gerb-ster/Vulcan-DCO/images/attiny programmer.jpeg

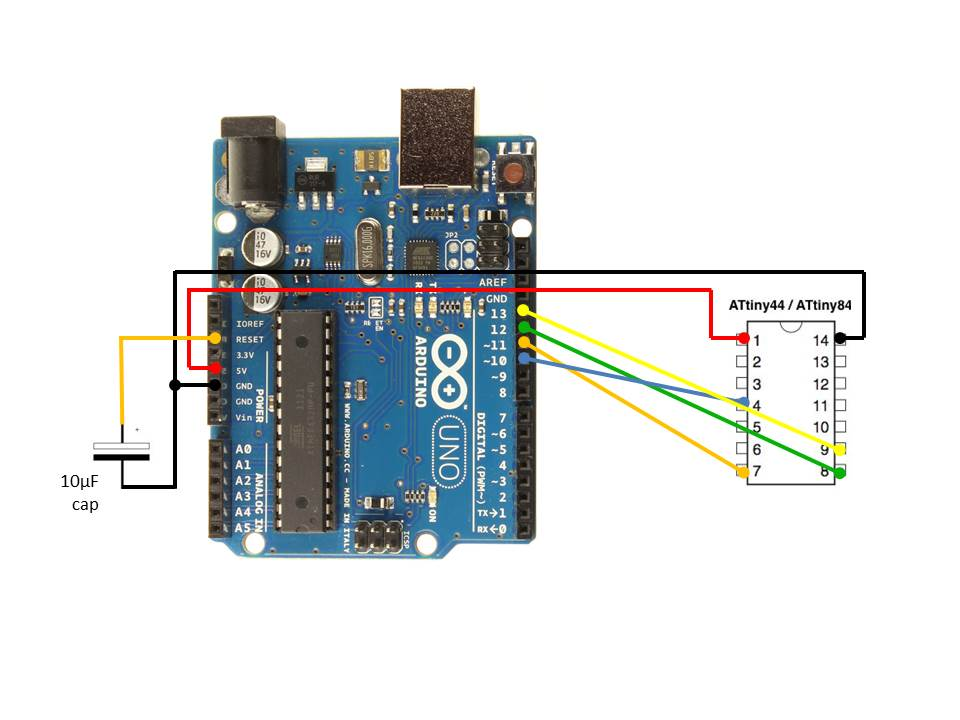
images/attiny programmer.jpeg
