gerb-ster/Vulcan-DCO/images/IMG_1315.jpeg

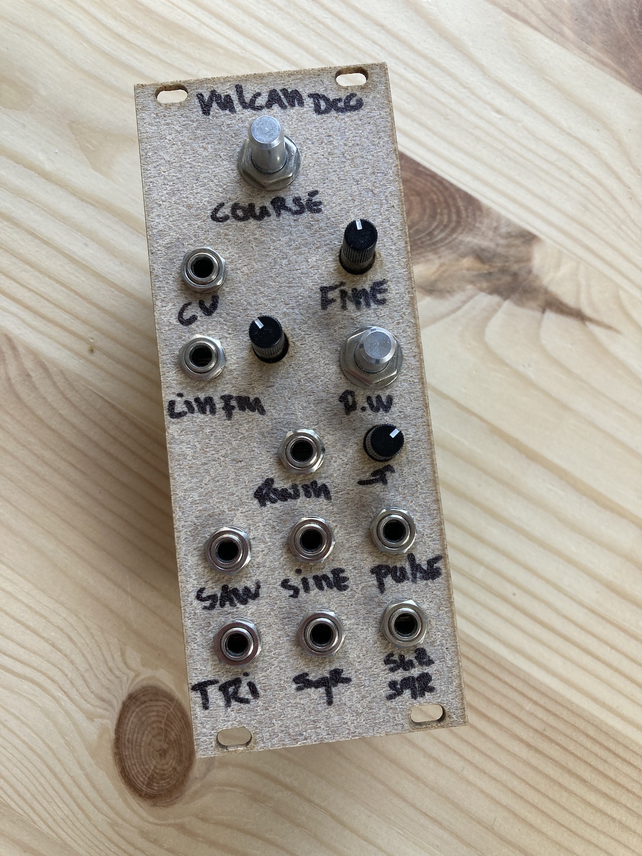
images/IMG_1315.jpeg
