gerb-ster/Vulcan-DCO/images/IMG_1316.jpeg

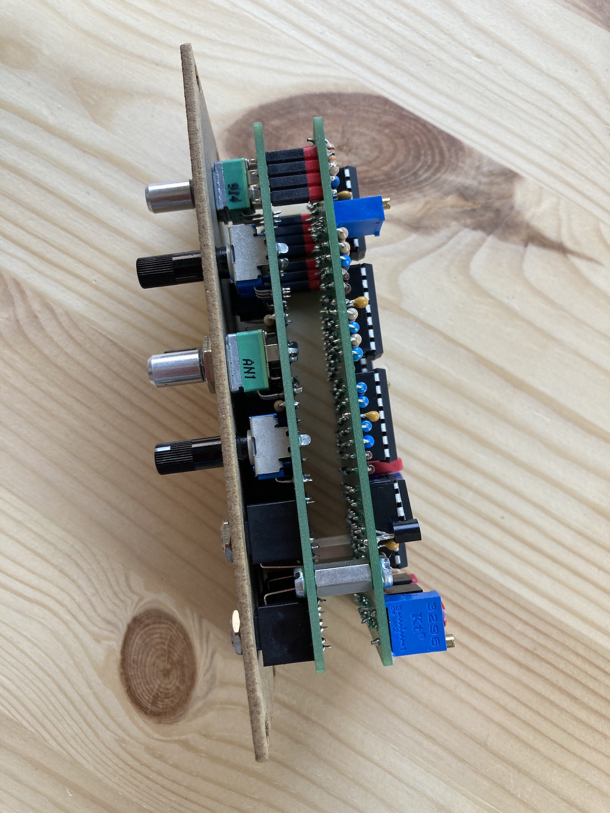
images/IMG_1316.jpeg
