gerb-ster/Vulcan-DCO/images/IMG_1317.jpeg

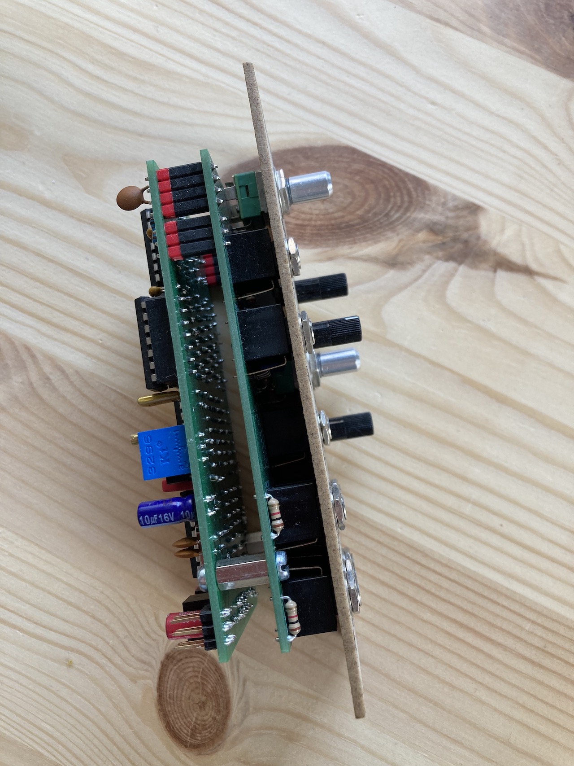
images/IMG_1317.jpeg
