gerb-ster/Vulcan-DCO/images/IMG_1318.jpeg

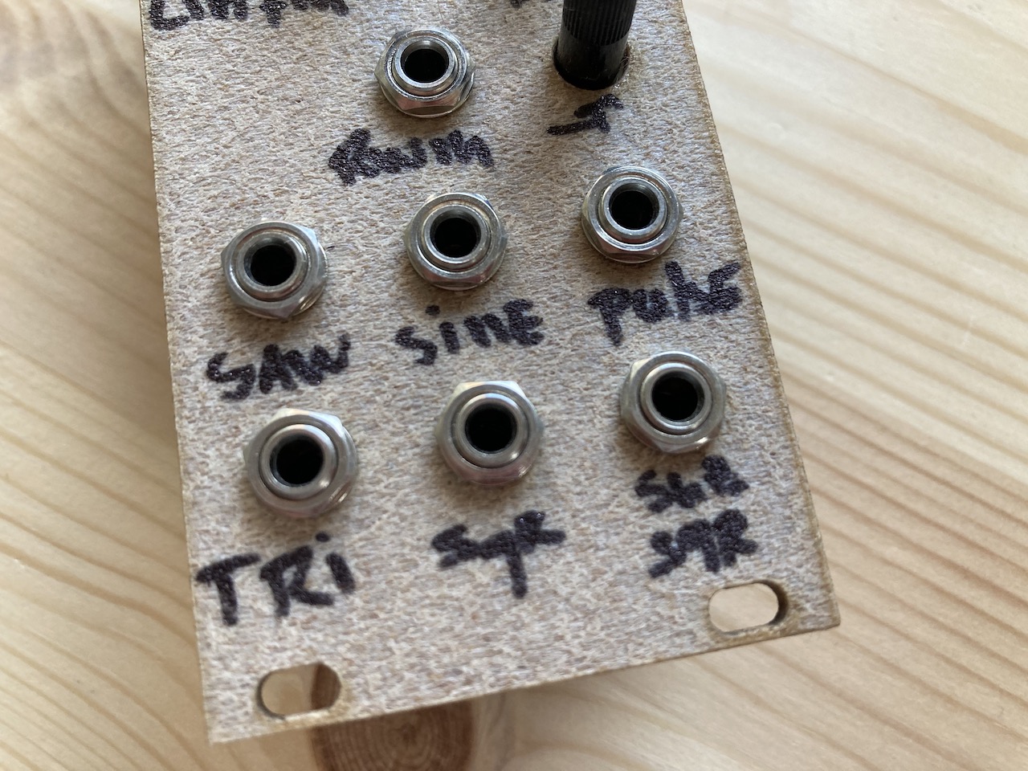
images/IMG_1318.jpeg
