gerb-ster/Vulcan-DCO/images/IMG_1319.jpeg

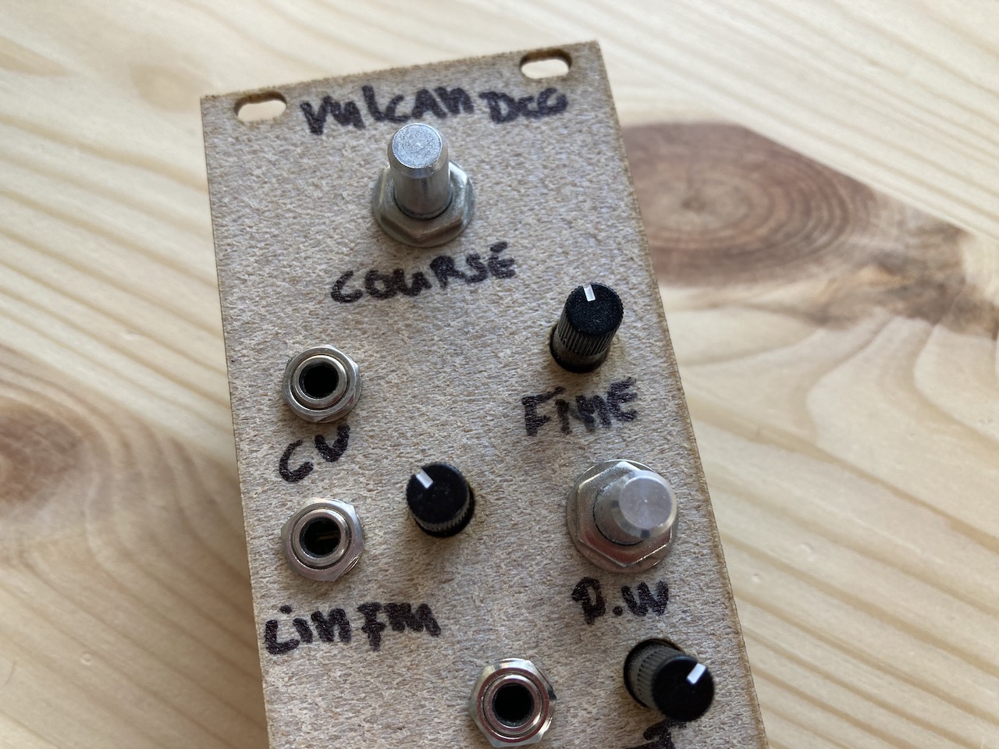
images/IMG_1319.jpeg
