gerb-ster/Vulcan-DCO/images/IMG_1320.jpeg

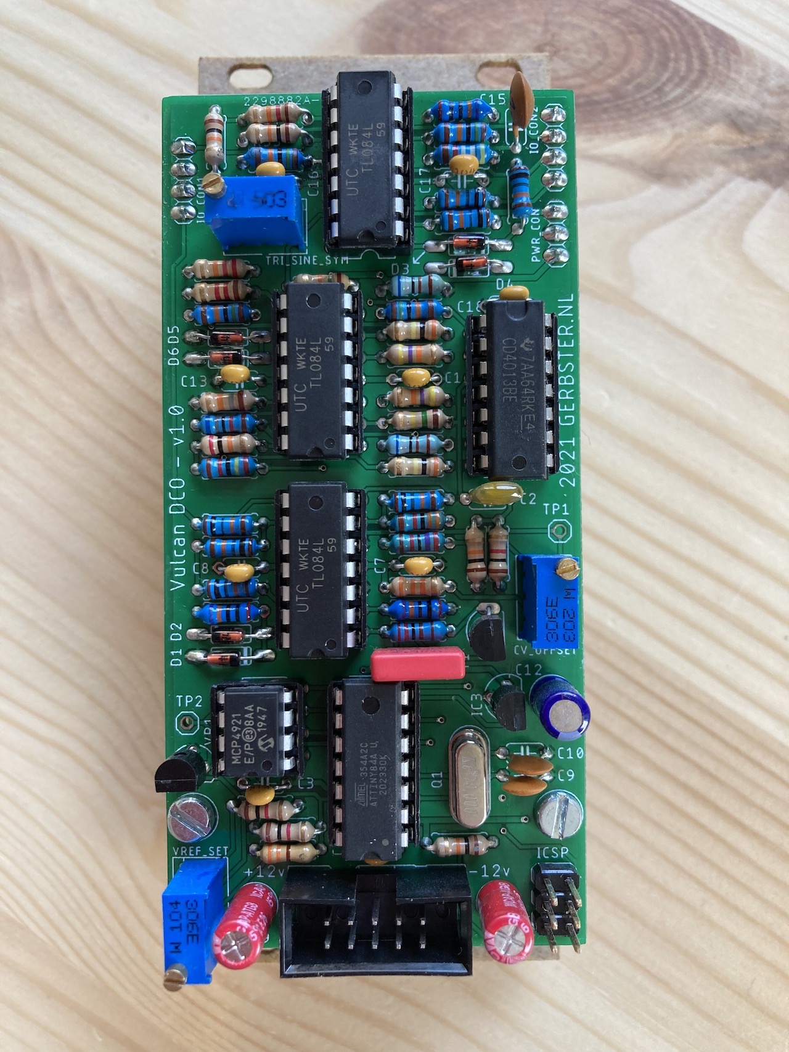
images/IMG_1320.jpeg
