gerb-ster/Vulcan-DCO/images/IMG_1321.jpeg

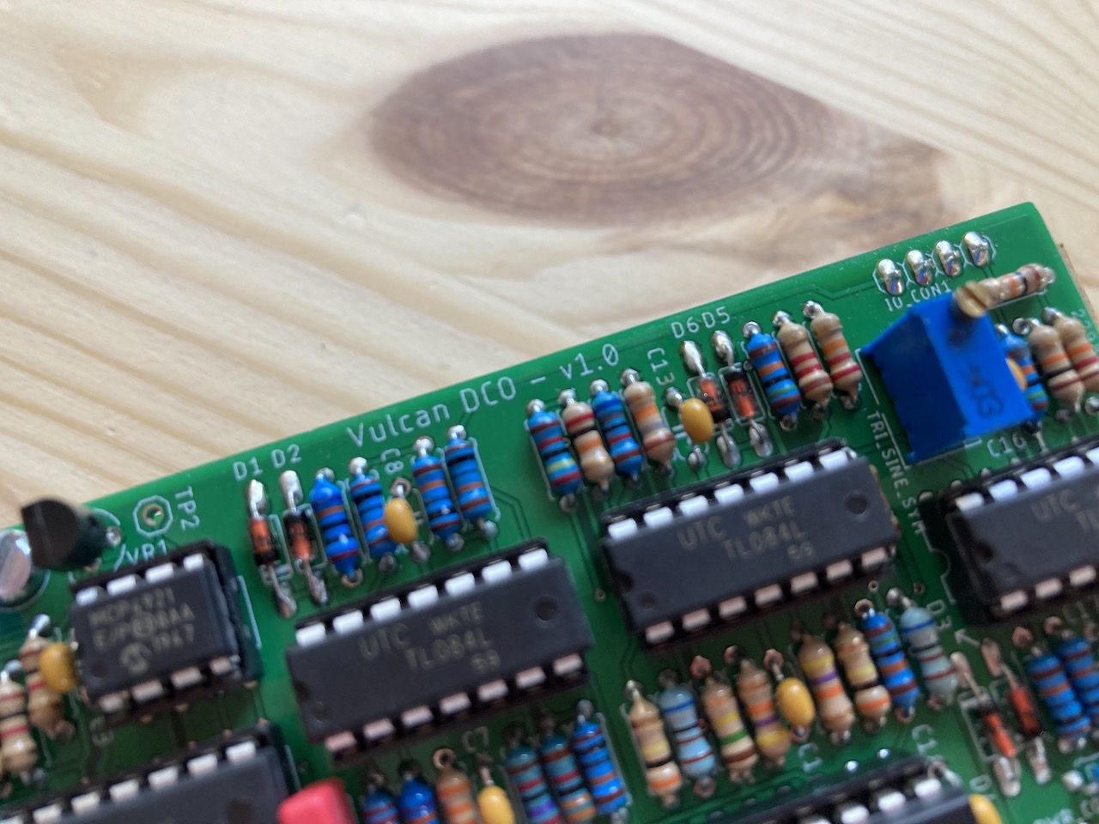
images/IMG_1321.jpeg
