gerb-ster/Vulcan-DCO/images/IMG_1322.jpeg

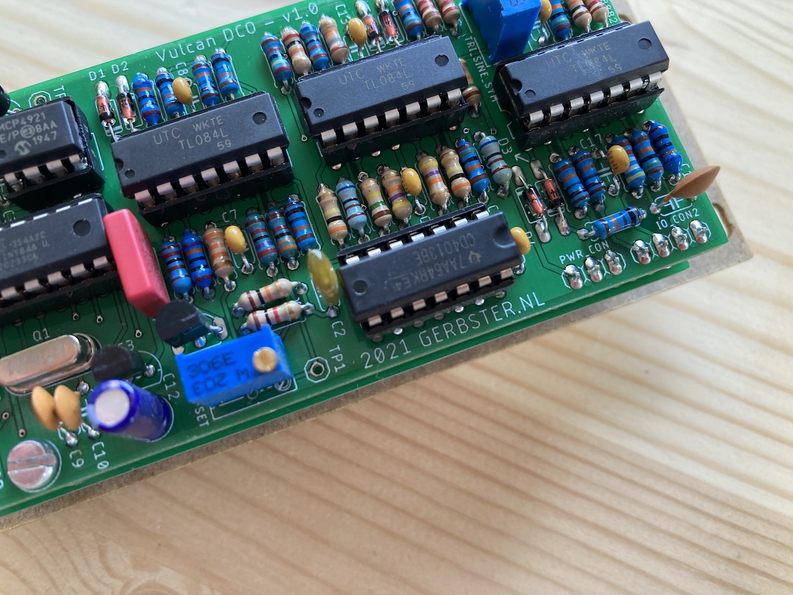
images/IMG_1322.jpeg
