gerb-ster/Vulcan-DCO/images/pulse.png

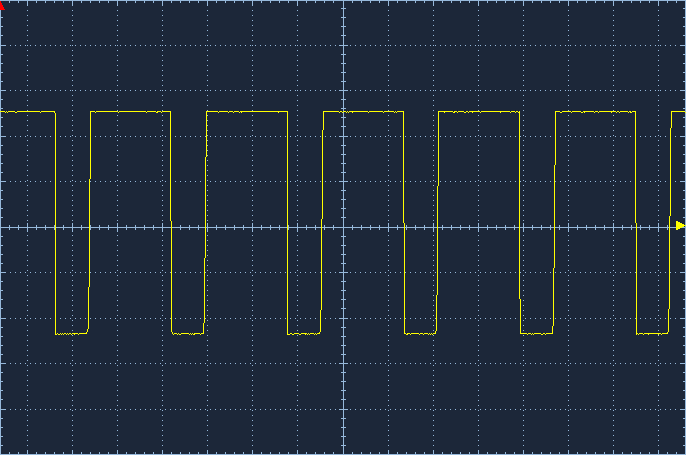
images/pulse.png
