gerb-ster/Vulcan-DCO/images/sine.png

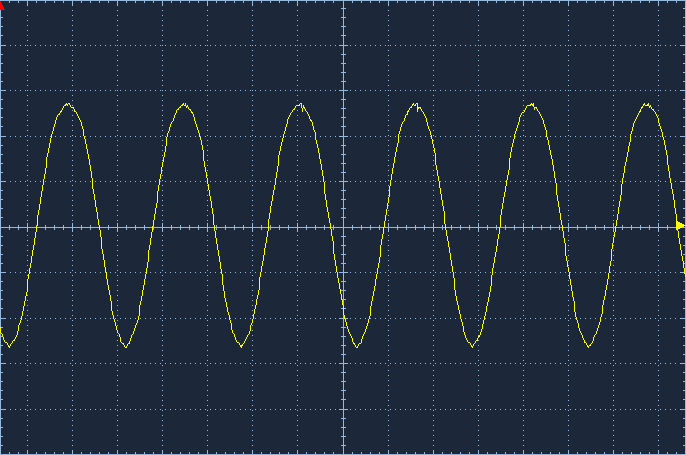
images/sine.png
