gerb-ster/Vulcan-DCO/images/sub-square.png

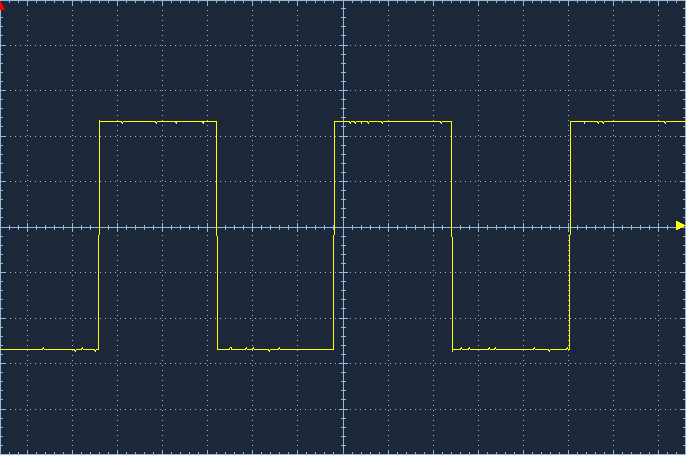
images/sub-square.png
