gerb-ster/Vulcan-DCO/images/triangle.png

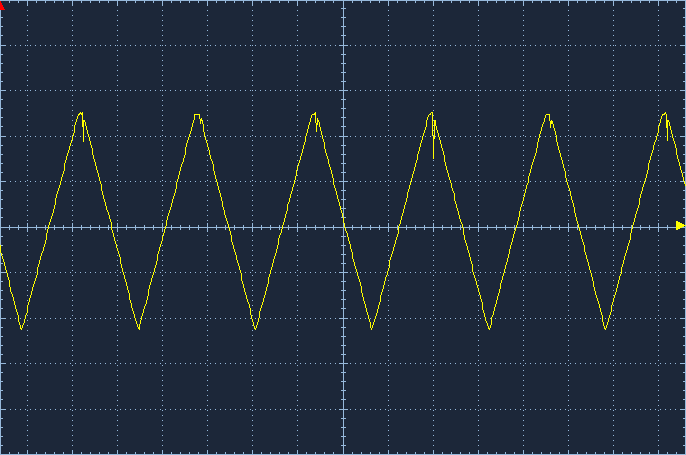
images/triangle.png
