gerb-ster/Vulcan-DCO/firmware/include/clock_frq_lookup.h

// clock frequencies lookup table


static const PROGMEM uint16_t frq_lookup[1024] = {	
	45455, 45209, 44965, 44722, 44481, 44240, 44001, 43764, 
	43527, 43292, 43059, 42826, 42595, 42365, 42136, 41908, 
	41682, 41457, 41233, 41010, 40789, 40569, 40349, 40132, 
	39915, 39699, 39485, 39272, 39060, 38849, 38639, 38430, 
	38223, 38016, 37811, 37607, 37404, 37202, 37001, 36801, 
	36602, 36404, 36208, 36012, 35818, 35624, 35432, 35241, 
	35050, 34861, 34673, 34485, 34299, 34114, 33930, 33746, 
	33564, 33383, 33203, 33023, 32845, 32668, 32491, 32316, 
	32141, 31968, 31795, 31623, 31452, 31283, 31114, 30946, 
	30779, 30612, 30447, 30283, 30119, 29956, 29795, 29634, 
	29474, 29314, 29156, 28999, 28842, 28686, 28531, 28377, 
	28224, 28072, 27920, 27769, 27619, 27470, 27322, 27174, 
	27027, 26881, 26736, 26592, 26448, 26305, 26163, 26022, 
	25882, 25742, 25603, 25464, 25327, 25190, 25054, 24919, 
	24784, 24650, 24517, 24385, 24253, 24122, 23992, 23862, 
	23733, 23605, 23478, 23351, 23225, 23100, 22975, 22851, 
	22727, 22605, 22482, 22361, 22240, 22120, 22001, 21882, 
	21764, 21646, 21529, 21413, 21297, 21182, 21068, 20954, 
	20841, 20728, 20617, 20505, 20394, 20284, 20175, 20066, 
	19957, 19850, 19742, 19636, 19530, 19424, 19319, 19215, 
	19111, 19008, 18905, 18803, 18702, 18601, 18500, 18400, 
	18301, 18202, 18104, 18006, 17909, 17812, 17716, 17620, 
	17525, 17430, 17336, 17243, 17150, 17057, 16965, 16873, 
	16782, 16691, 16601, 16512, 16423, 16334, 16246, 16158, 
	16071, 15984, 15897, 15812, 15726, 15641, 15557, 15473, 
	15389, 15306, 15223, 15141, 15060, 14978, 14897, 14817, 
	14737, 14657, 14578, 14499, 14421, 14343, 14266, 14189, 
	14112, 14036, 13960, 13885, 13810, 13735, 13661, 13587, 
	13514, 13441, 13368, 13296, 13224, 13153, 13082, 13011, 
	12941, 12871, 12801, 12732, 12663, 12595, 12527, 12459, 
	12392, 12325, 12259, 12192, 12127, 12061, 11996, 11931, 
	11867, 11803, 11739, 11676, 11612, 11550, 11487, 11425, 
	11364, 11302, 11241, 11181, 11120, 11060, 11000, 10941, 
	10882, 10823, 10765, 10707, 10649, 10591, 10534, 10477, 
	10421, 10364, 10308, 10253, 10197, 10142, 10087, 10033, 
	9979, 9925, 9871, 9818, 9765, 9712, 9660, 9608, 
	9556, 9504, 9453, 9402, 9351, 9300, 9250, 9200, 
	9151, 9101, 9052, 9003, 8954, 8906, 8858, 8810, 
	8763, 8715, 8668, 8621, 8575, 8528, 8482, 8437, 
	8391, 8346, 8301, 8256, 8211, 8167, 8123, 8079, 
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
};
